JobyCheng/FYP-Smart-Light-Switch/Switch/include/switch_motor.h

#ifndef SWITCH_MOTOR_H
#define SWITCH_MOTOR_H

#include <Arduino.h>
#include "switch_gy25z.h"
#include "switch_touch.h"
#include <Preferences.h>
#include "soc/timer_group_struct.h"
#include "soc/timer_group_reg.h"

extern Preferences preferences;

//motor control pins
extern const int AIN1; 
extern const int AIN2; 
extern const int EN;

extern volatile float T8roll;
extern volatile float T9roll;

extern bool calManual;

void on();
void off();
void calibrate();
void manual_switch();
void turnClkwise();
void turnAntiClkwise();

#endif
